DoubleU-ANG/Dissertation/Picture/color sensor.png

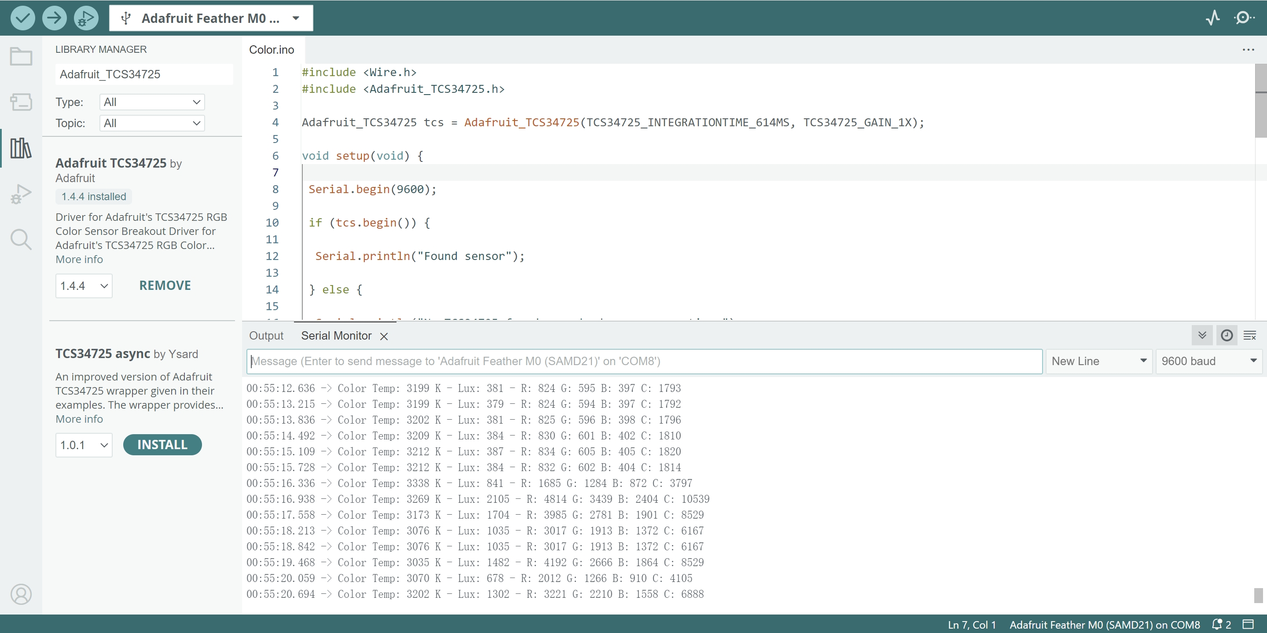
Picture/color sensor.png
