DoubleU-ANG/Dissertation/Picture/PCB12.jpg

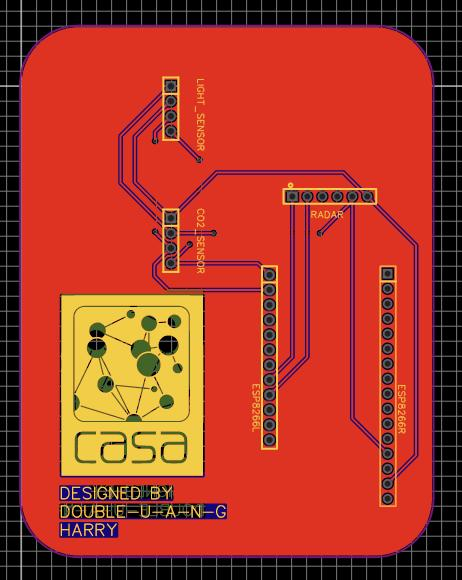
Picture/PCB12.jpg
