DoubleU-ANG/Dissertation/Picture/pcb22.jpg

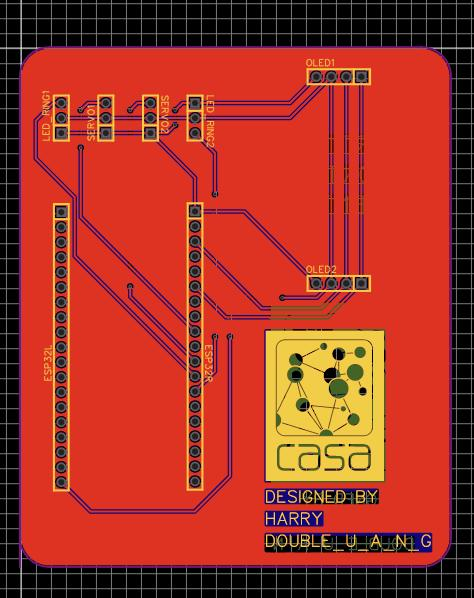
Picture/pcb22.jpg
