DoubleU-ANG/Dissertation/Picture/sensor data.png

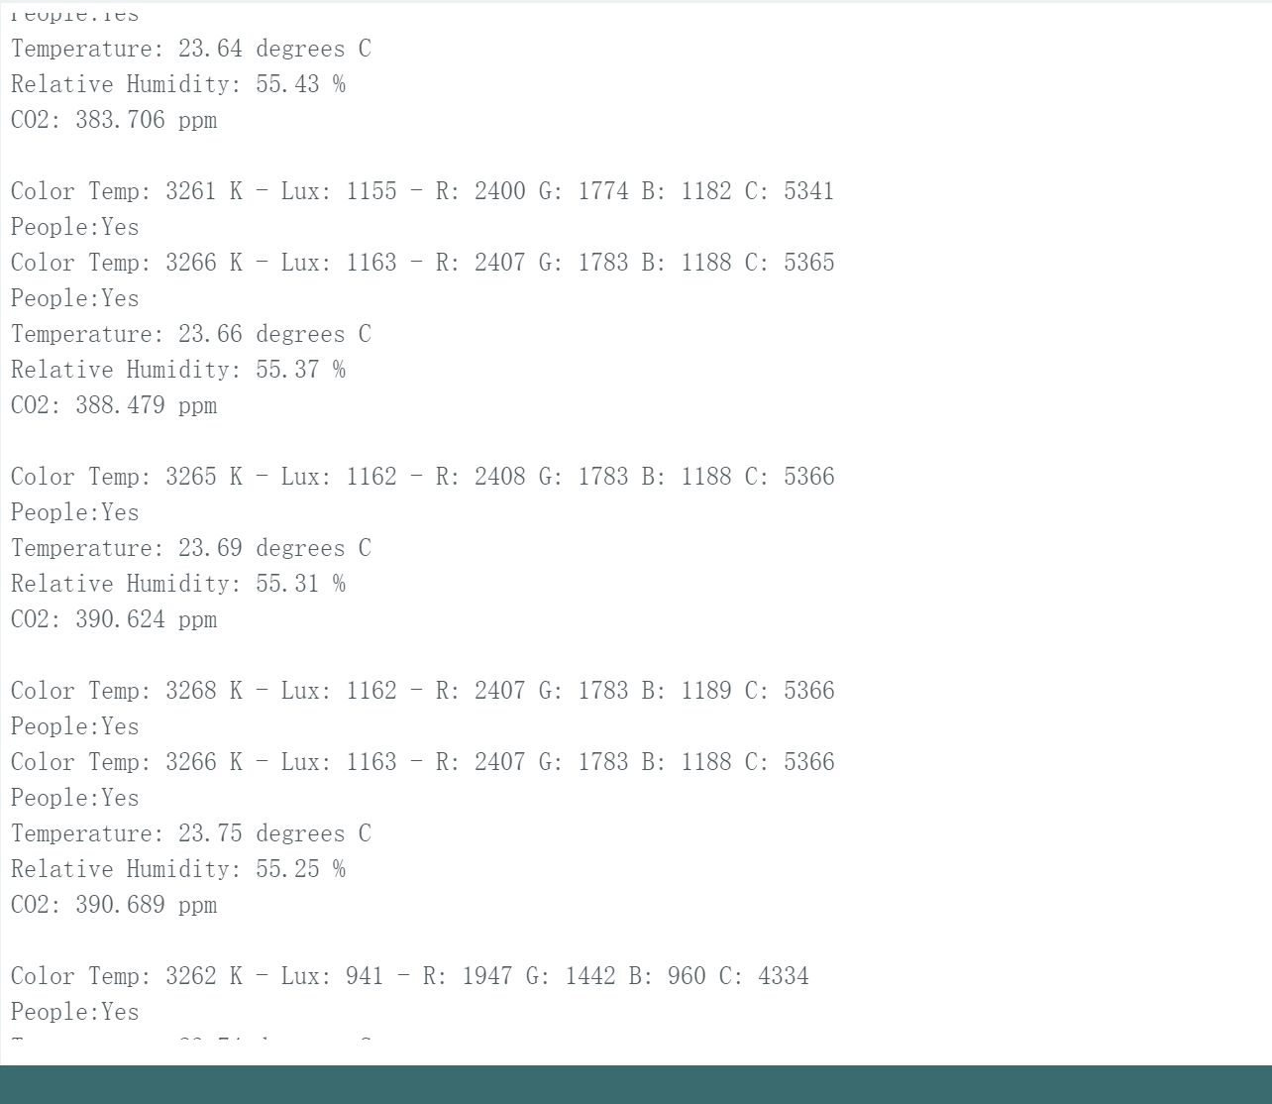
Picture/sensor data.png
